Umi4Life/NAGEKI-3.33/LEVER/toximango/Spur Gear (12 teeth) knurled.stl

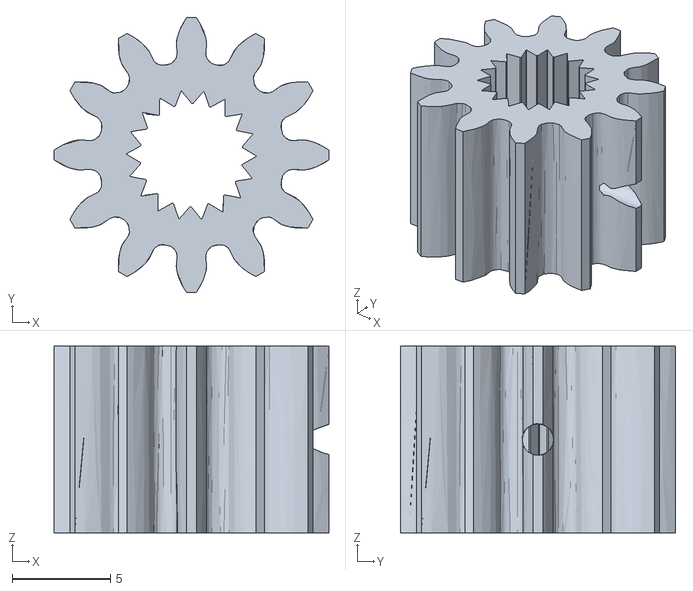
[picture p27: CAD file, 2022-10-10]
LEVER/toximango/Spur Gear (12 teeth) knurled.stl
14.0 x 14.0 x 9.50
