Umi4Life/NAGEKI-3.33/PCB/ONGEKI PCB.step

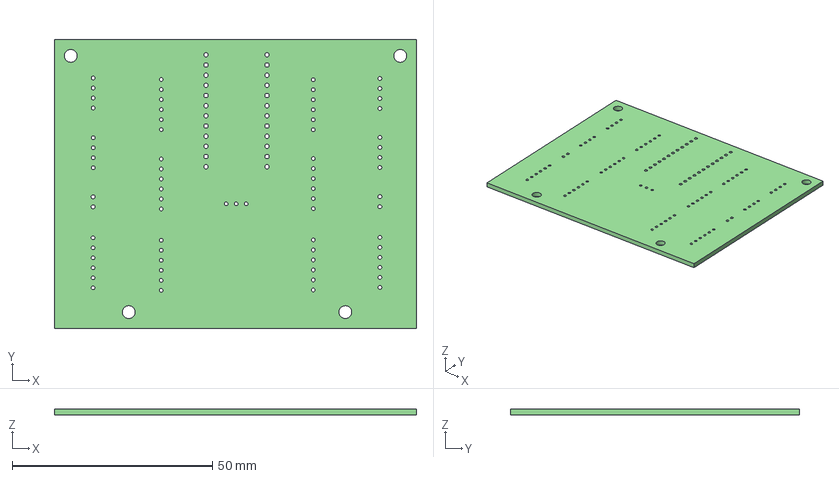
[picture p28: CAD file, 2022-10-10]
PCB/ONGEKI PCB.step
90.4 x 72.1 x 1.60 mm
