Umi4Life/NAGEKI-3.33/WAD/backplate right.stl

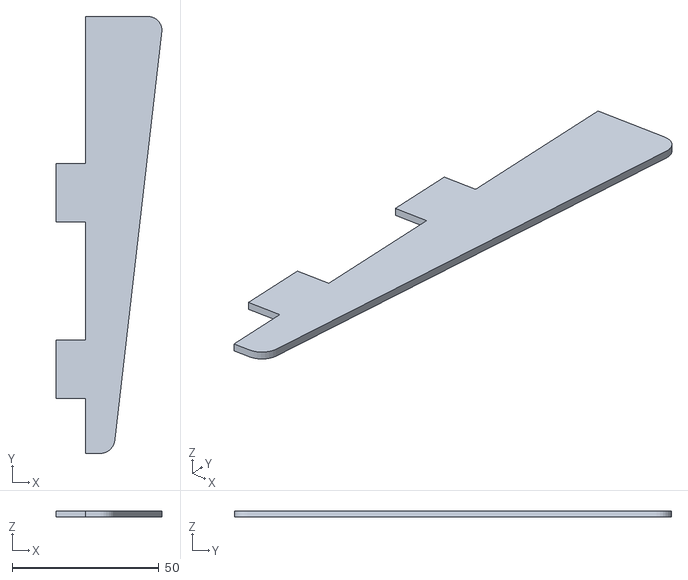
[picture p29: CAD file, 2022-10-10]
WAD/backplate right.stl
36.0 x 148.7 x 2.00
