Umi4Life/NAGEKI-3.33/CASE/sides/side south.dxf

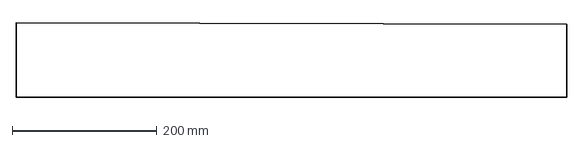
[picture p30: CAD file, 2022-10-10]
CASE/sides/side south.dxf
760.0 x 103.0 mm
