Umi4Life/NAGEKI-3.33/CASE/top/top.dxf

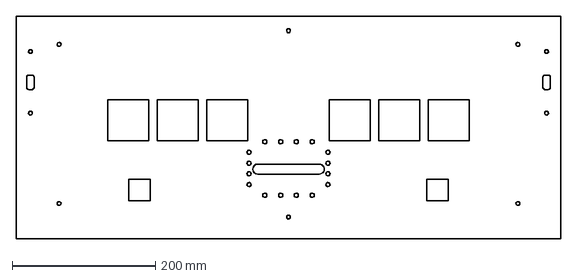
[picture p31: CAD file, 2022-10-10]
CASE/top/top.dxf
760.0 x 310.0 mm
