Umi4Life/NAGEKI-3.33/CASE/wad/wad s.stl

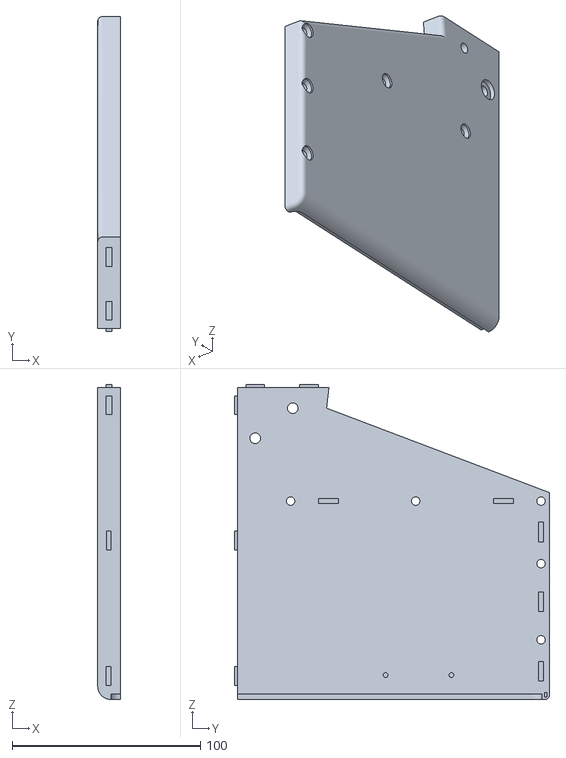
[picture p32: CAD file, 2022-10-10]
CASE/wad/wad s.stl
12.0 x 167.5 x 167.5
