Umi4Life/NAGEKI-3.33/LEVER/toximango/lever big.stl

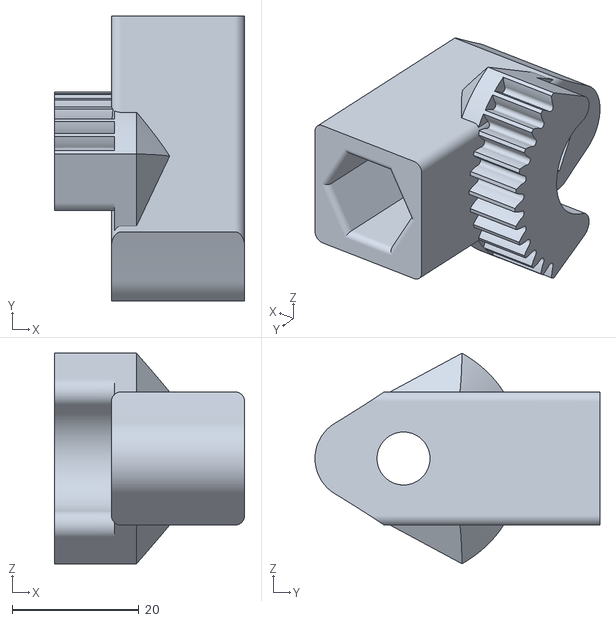
[picture p33: CAD file, 2022-10-10]
LEVER/toximango/lever big.stl
30.0 x 45.0 x 33.2
