Umi4Life/NAGEKI-3.33/WAD/sensor mount 3mm.stl

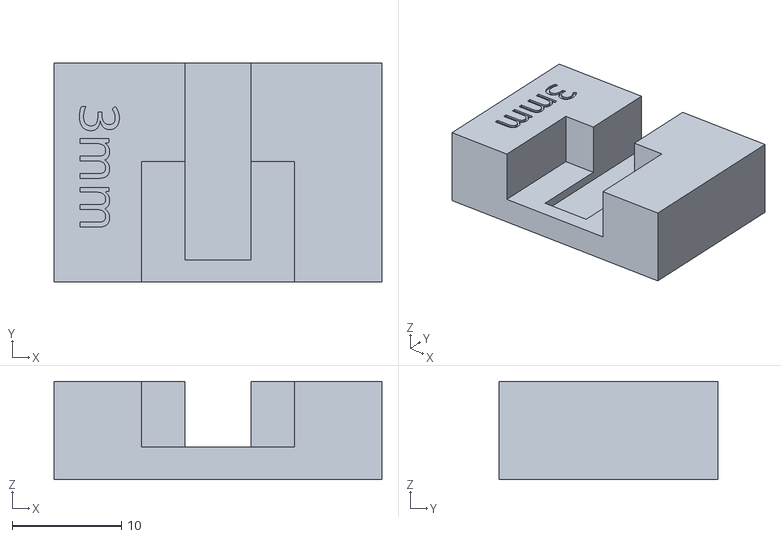
[picture p34: CAD file, 2022-10-10]
WAD/sensor mount 3mm.stl
30.0 x 20.0 x 9.00
