Umi4Life/NAGEKI-3.33/CASE/bottom/bottom.dxf

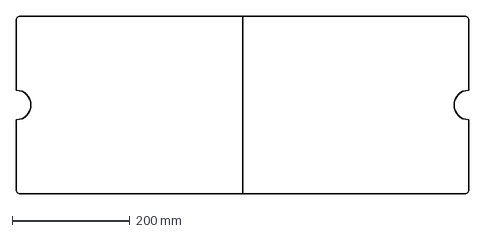
[picture p35: CAD file, 2022-10-10]
CASE/bottom/bottom.dxf
769.4 x 301.4 mm
