Umi4Life/NAGEKI-3.33/CASE/top/top q.stl

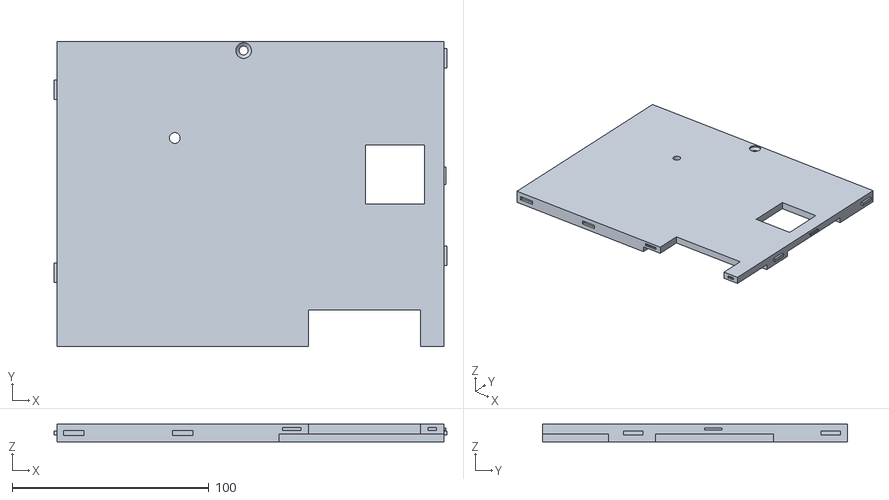
[picture p36: CAD file, 2022-10-10]
CASE/top/top q.stl
200.0 x 155.0 x 9.00
