Umi4Life/NAGEKI-3.33/CASE/wad/wad q .stl

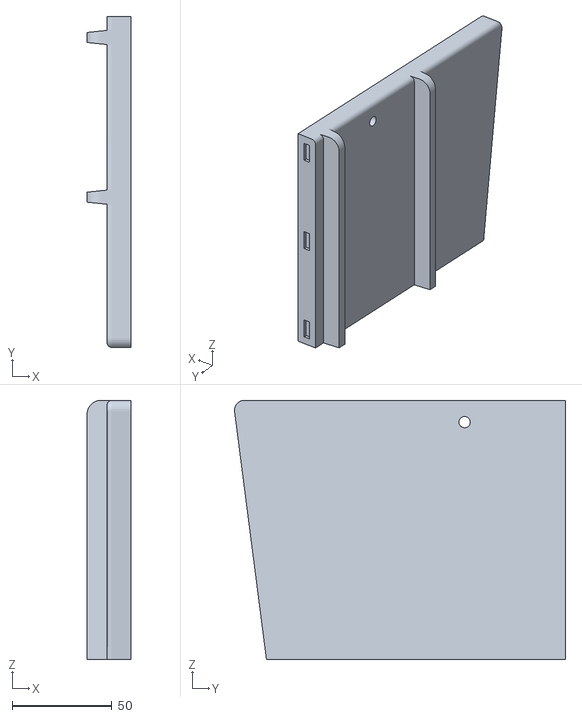
[picture p37: CAD file, 2022-10-10]
CASE/wad/wad q .stl
22.0 x 165.7 x 129.8
