Umi4Life/NAGEKI-3.33/WAD/backplate setsuna.stl

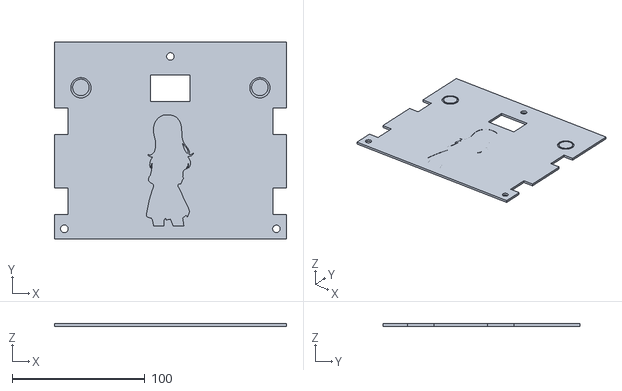
[picture p38: CAD file, 2022-10-10]
WAD/backplate setsuna.stl
175.0 x 148.7 x 2.00
