Umi4Life/NAGEKI-3.33/CASE/wad/wad a.stl

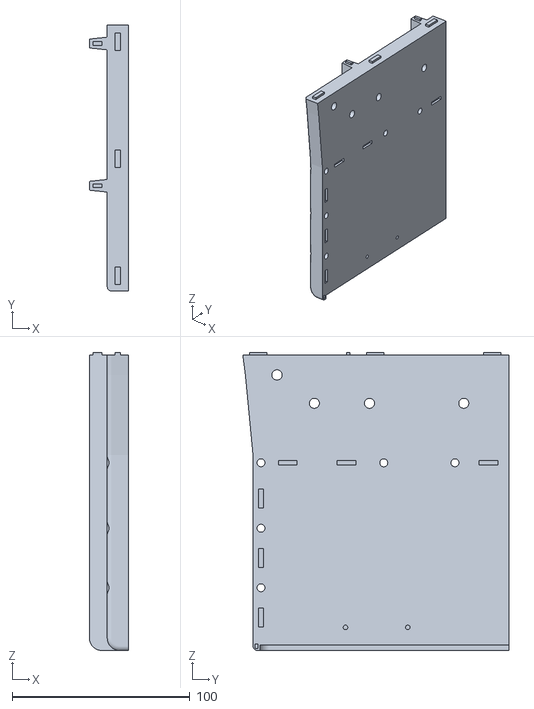
[picture p39: CAD file, 2022-10-10]
CASE/wad/wad a.stl
22.0 x 149.7 x 167.5
