Umi4Life/NAGEKI-3.33/WAD/sensor mount 7mm.stl

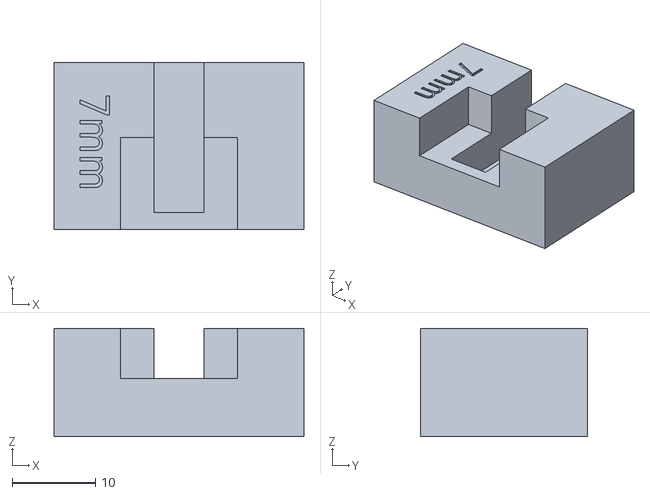
[picture p40: CAD file, 2022-10-10]
WAD/sensor mount 7mm.stl
30.0 x 20.0 x 13.0
