Umi4Life/NAGEKI-3.33/WAD/sensor mount 4mm.stl

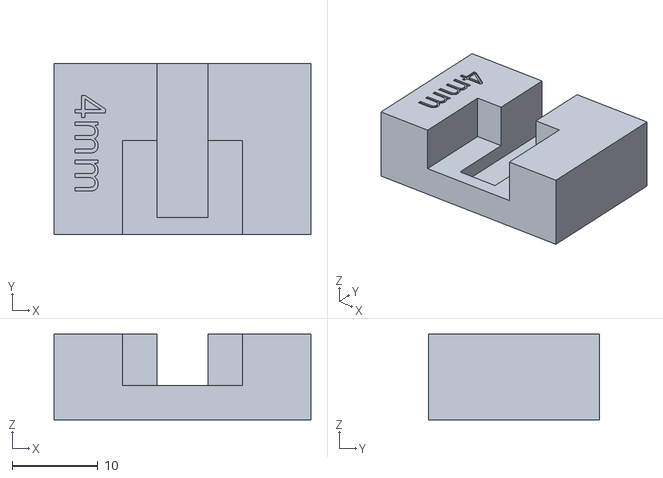
[picture p41: CAD file, 2022-10-10]
WAD/sensor mount 4mm.stl
30.0 x 20.0 x 10.00
