Umi4Life/NAGEKI-3.33/CASE/top/top w.stl

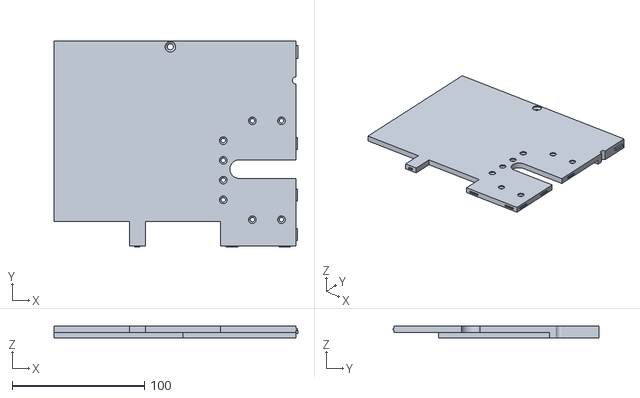
[picture p42: CAD file, 2022-10-10]
CASE/top/top w.stl
184.5 x 156.0 x 9.00
