Umi4Life/NAGEKI-3.33/WAD/backplate left.stl

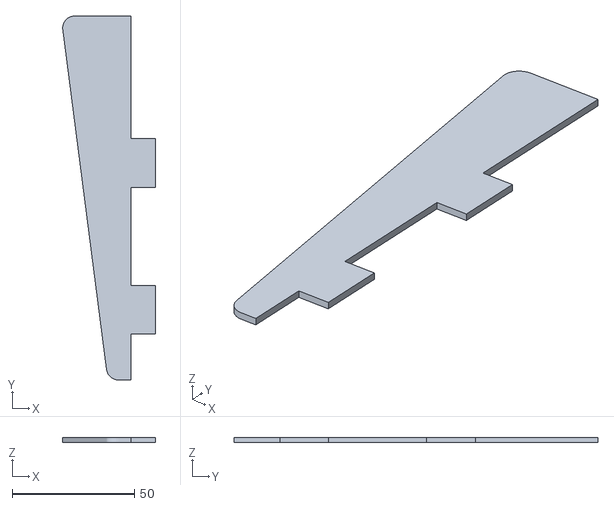
[picture p43: CAD file, 2022-10-10]
WAD/backplate left.stl
37.8 x 148.7 x 2.00
