Umi4Life/NAGEKI-3.33/WAD/sensor mount 5mm.stl

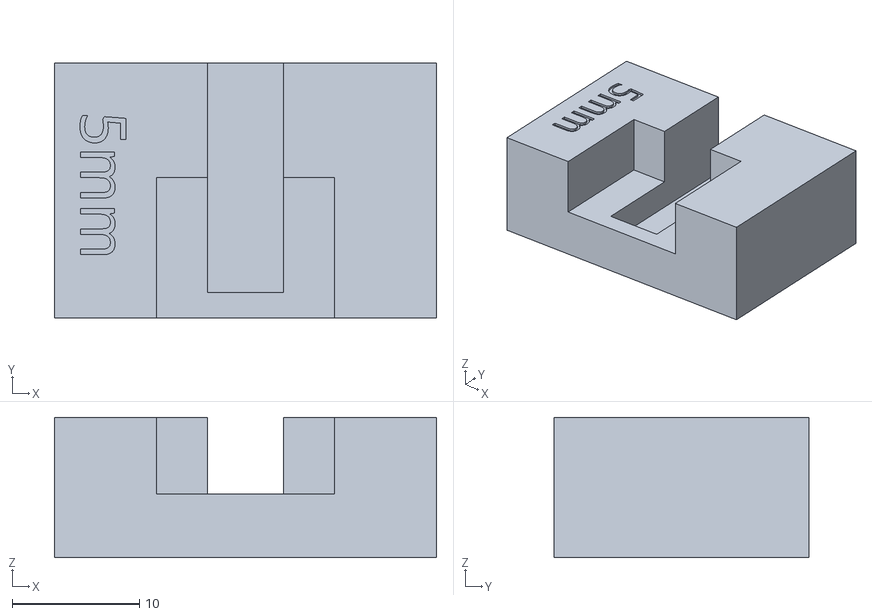
[picture p44: CAD file, 2022-10-10]
WAD/sensor mount 5mm.stl
30.0 x 20.0 x 11.0
