Umi4Life/NAGEKI-3.33/WAD/sensor mount 6mm.stl

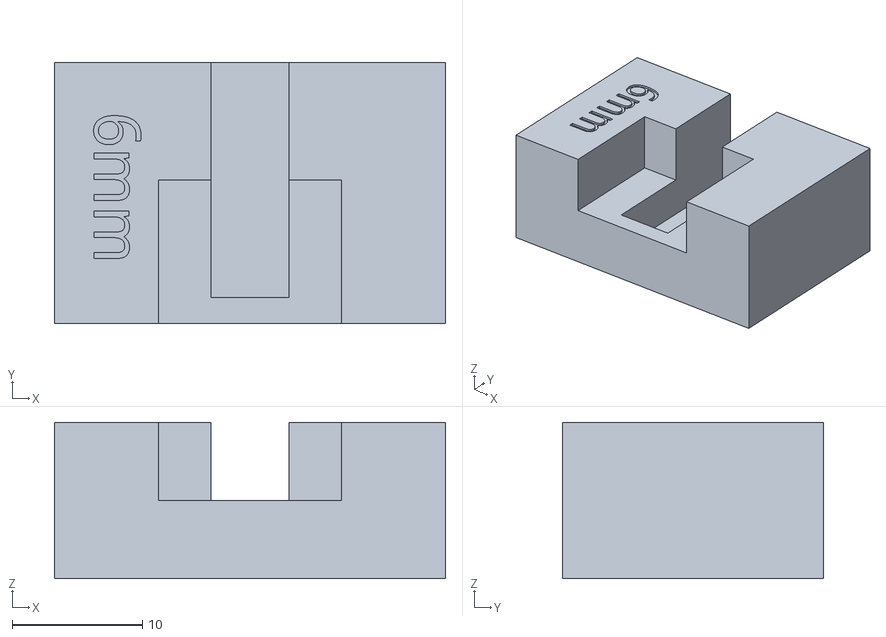
[picture p45: CAD file, 2022-10-10]
WAD/sensor mount 6mm.stl
30.0 x 20.0 x 12.0
