Umi4Life/NAGEKI-3.33/WAD/wad cover.stl

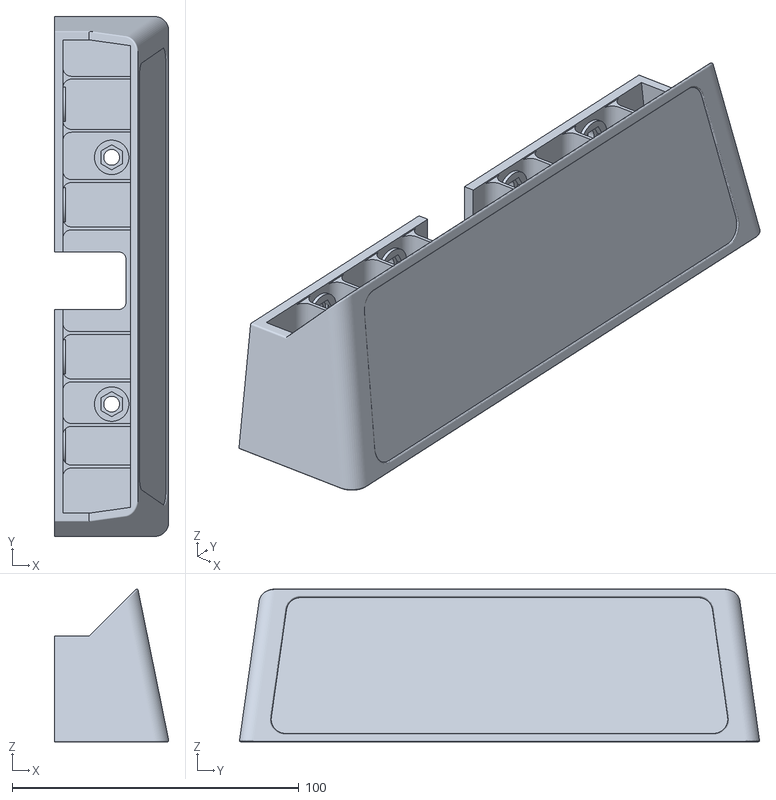
[picture p46: CAD file, 2022-08-31]
WAD/wad cover.stl
39.9 x 181.2 x 53.3
