Umi4Life/NAGEKI-3.33/WAD/ONGEKI WAD shield.stl

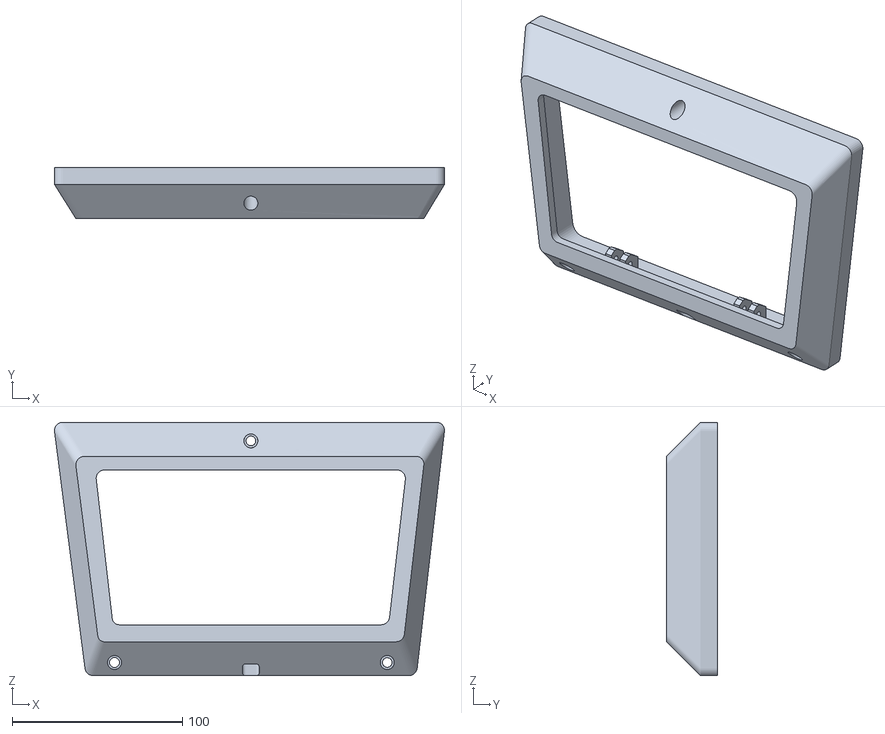
[picture p47: CAD file, 2022-06-08]
WAD/ONGEKI WAD shield.stl
228.8 x 30.0 x 148.7
