Umi4Life/NAGEKI-3.33/WAD/ONGEKI WAD button.stl

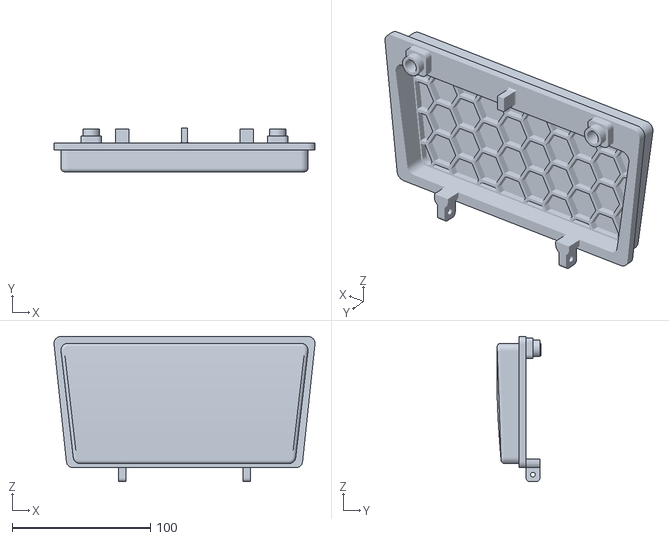
[picture p48: CAD file, 2022-06-08]
WAD/ONGEKI WAD button.stl
188.8 x 32.2 x 105.0
